adarshaudupa/Road_Surface_Monitoring_Device/model-design/Front Wheel Axle.jpeg

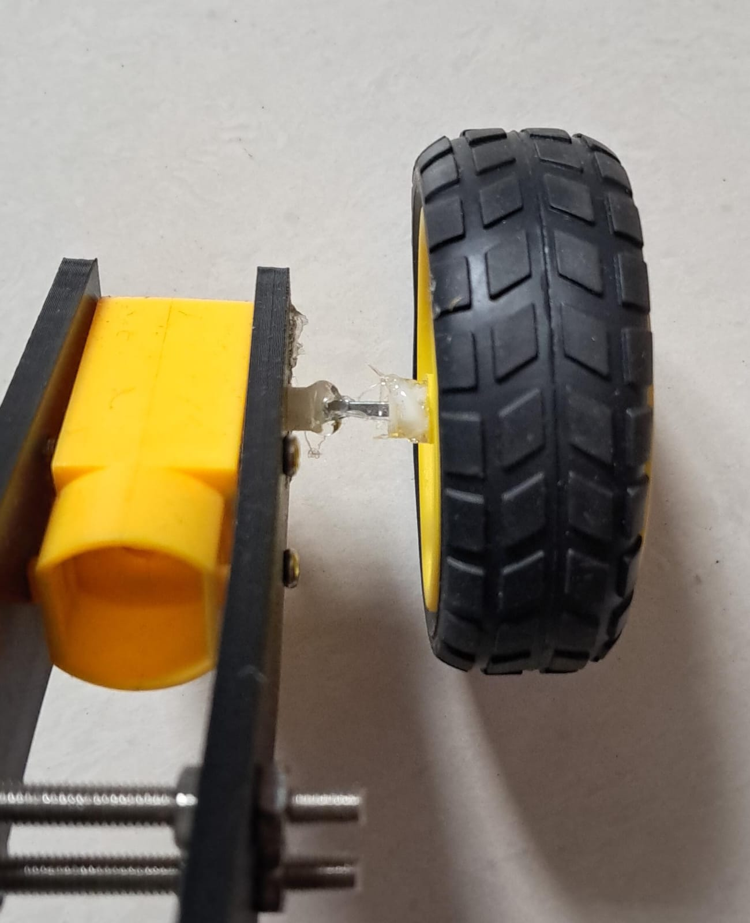
model-design/Front Wheel Axle.jpeg
